Zggis/micromouse-3d/maze/supports/elevated-cell_61.STEP

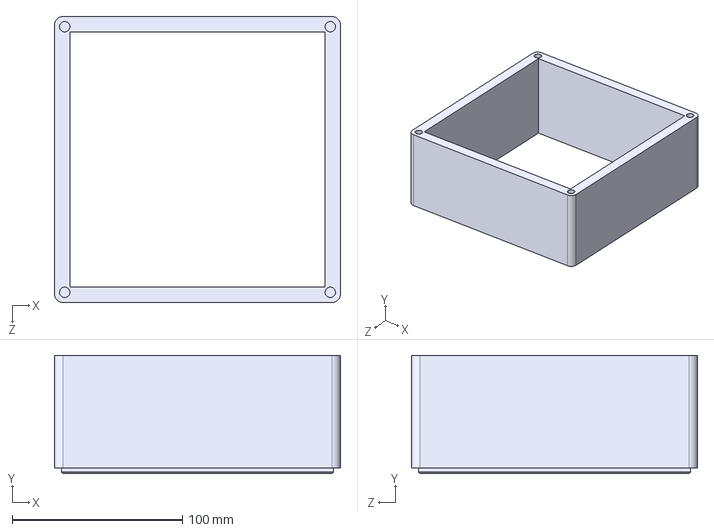
[picture p39: CAD file, 2026-06-22]
maze/supports/elevated-cell_61.STEP
168.0 x 69.4 x 168.0 mm
