Zggis/micromouse-3d/rules/pyramid.STL

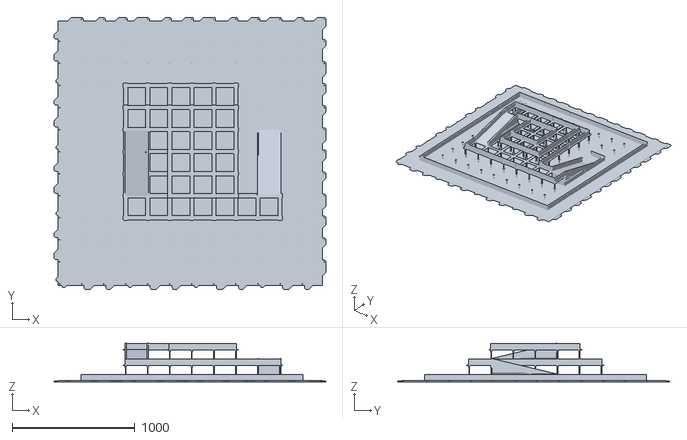
[picture p41: CAD file, 2026-09-28]
rules/pyramid.STL
2220.0 x 2220.0 x 317.4
