Zggis/micromouse-3d/maze/lattice/vertex_61.STEP

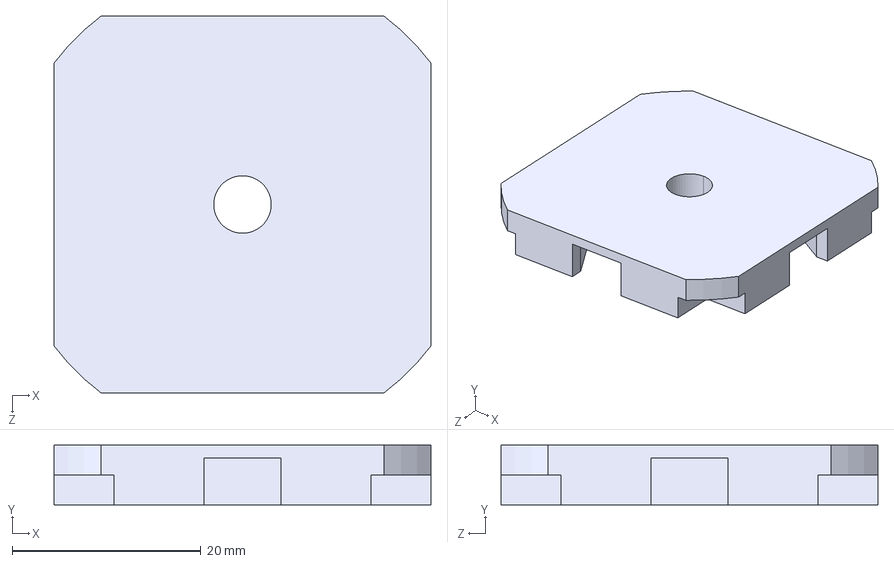
[picture p42: CAD file, 2026-06-22]
maze/lattice/vertex_61.STEP
40.0 x 6.35 x 40.0 mm
