Zggis/micromouse-3d/maze/ramp/ramp-middle-frame_62.STEP

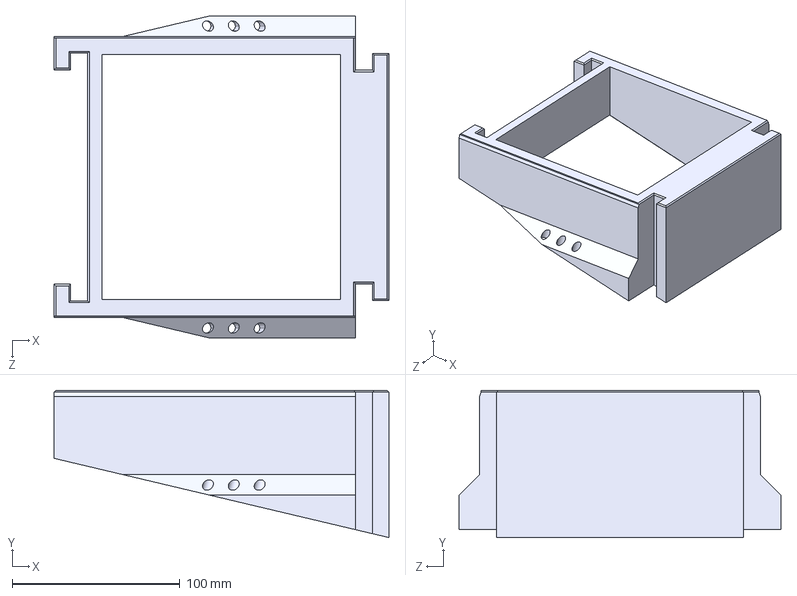
[picture p43: CAD file, 2026-07-10]
maze/ramp/ramp-middle-frame_62.STEP
199.6 x 87.7 x 192.0 mm
