Zggis/micromouse-3d/maze/supports/elevated-cell-top_61.STEP

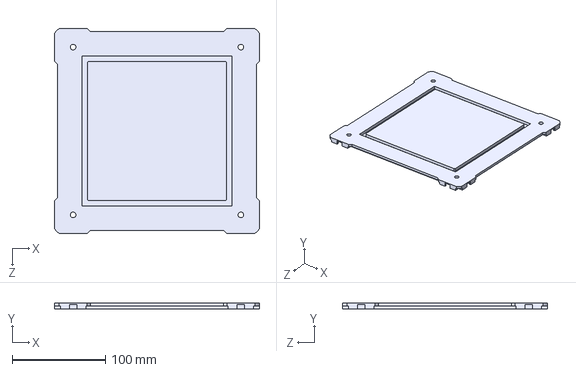
[picture p44: CAD file, 2026-06-22]
maze/supports/elevated-cell-top_61.STEP
220.0 x 6.35 x 220.0 mm
