Zggis/micromouse-3d/maze/walls/ramp-wall-upper.STEP

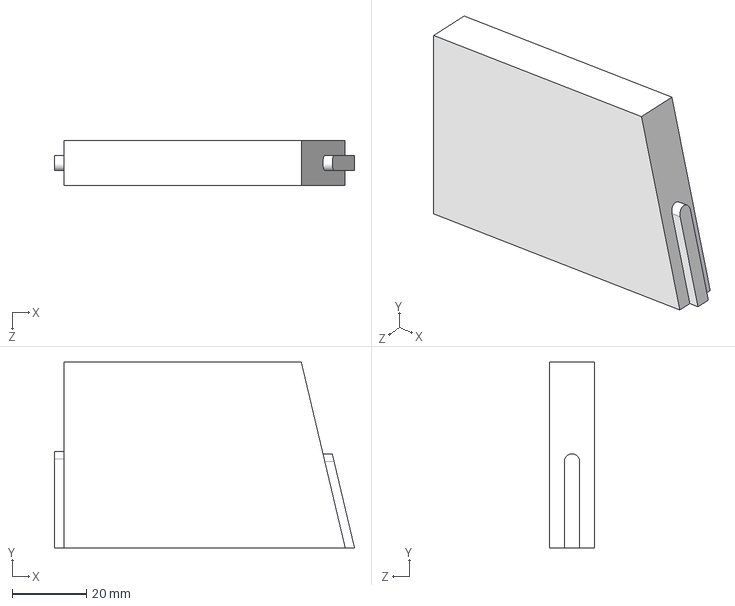
[picture p45: CAD file, 2026-06-22]
maze/walls/ramp-wall-upper.STEP
80.8 x 50.0 x 12.0 mm
