Zggis/micromouse-3d/maze/ramp/ramp-middle_62.STEP

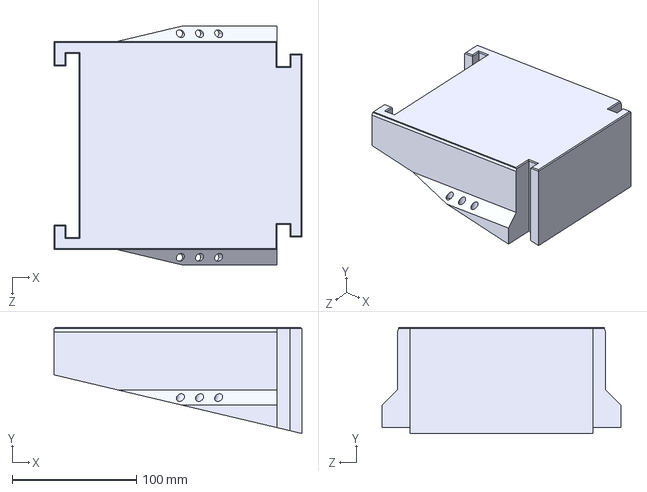
[picture p46: CAD file, 2026-07-10]
maze/ramp/ramp-middle_62.STEP
199.6 x 85.3 x 192.0 mm
