Zggis/micromouse-3d/maze/special/ramp-wall-half_60.STEP

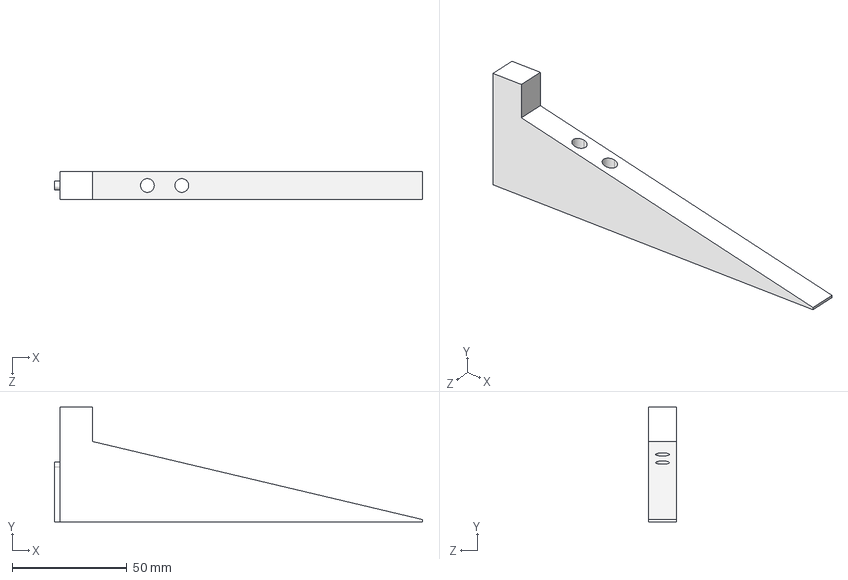
[picture p47: CAD file, 2026-06-22]
maze/special/ramp-wall-half_60.STEP
160.4 x 50.0 x 12.0 mm
