Zggis/micromouse-3d/maze/walls/ramp-wall-lower_62.STEP

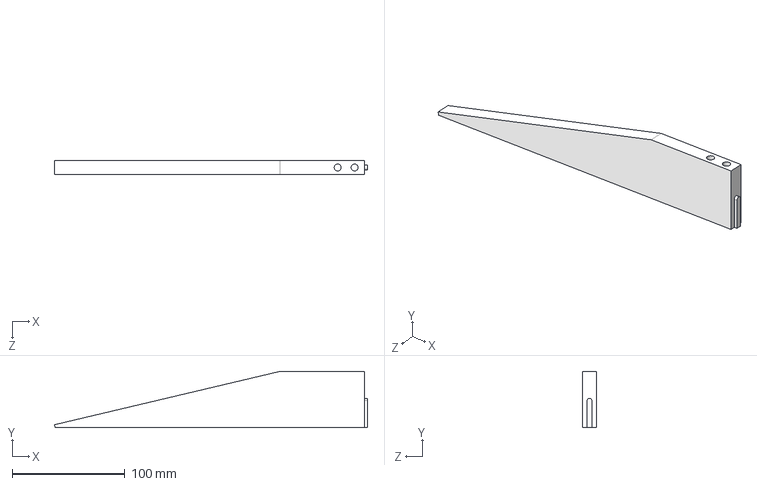
[picture p48: CAD file, 2026-06-22]
maze/walls/ramp-wall-lower_62.STEP
277.9 x 50.0 x 12.0 mm
