Zggis/micromouse-3d/maze/ramp/ramp-upper-frame_60.STEP

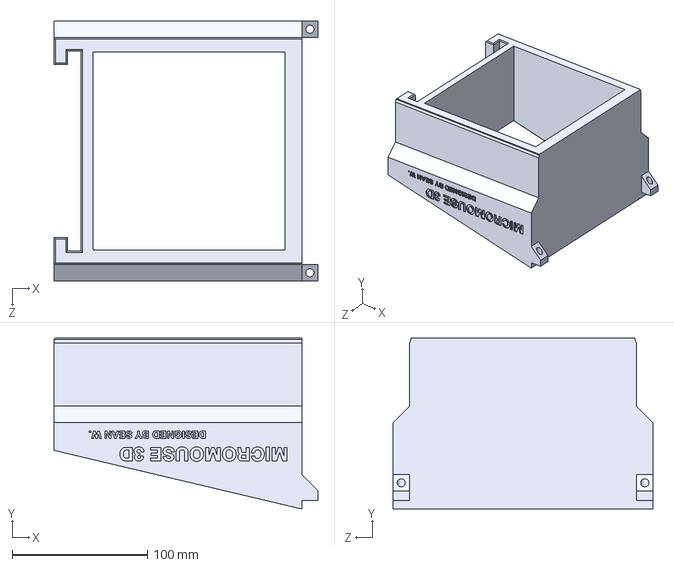
[picture p49: CAD file, 2026-07-10]
maze/ramp/ramp-upper-frame_60.STEP
195.1 x 126.3 x 192.0 mm
