Zggis/micromouse-3d/maze/special/ramp-wall-lower-hole_62.STEP

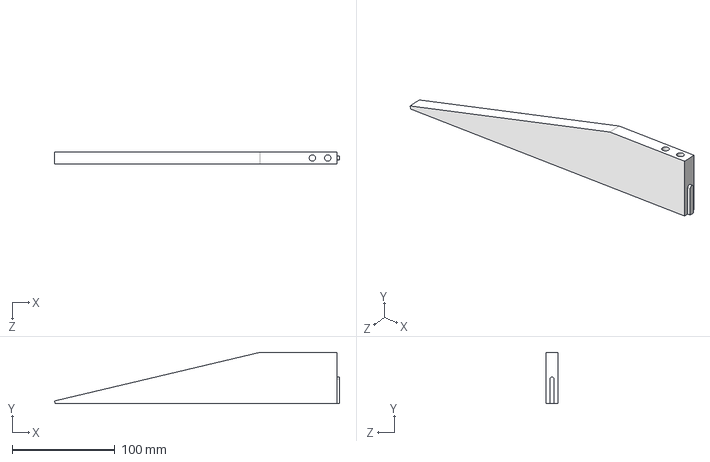
[picture p50: CAD file, 2026-06-22]
maze/special/ramp-wall-lower-hole_62.STEP
277.9 x 50.0 x 12.0 mm
