Zggis/micromouse-3d/maze/edges/connector-edge.STEP

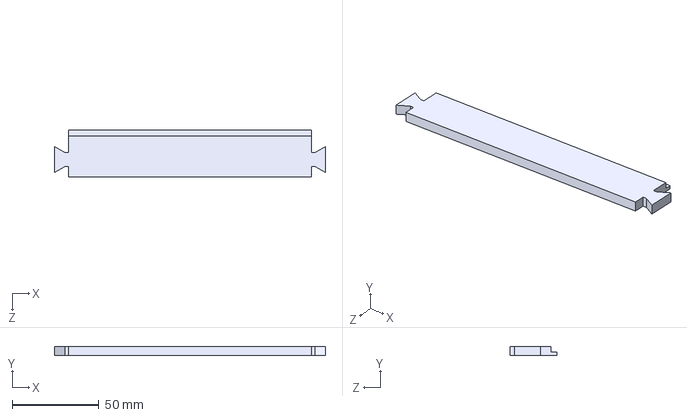
[picture p51: CAD file, 2026-06-22]
maze/edges/connector-edge.STEP
155.8 x 5.00 x 27.0 mm
