Zggis/micromouse-3d/maze/supports/elevated-cell-base_62.STEP

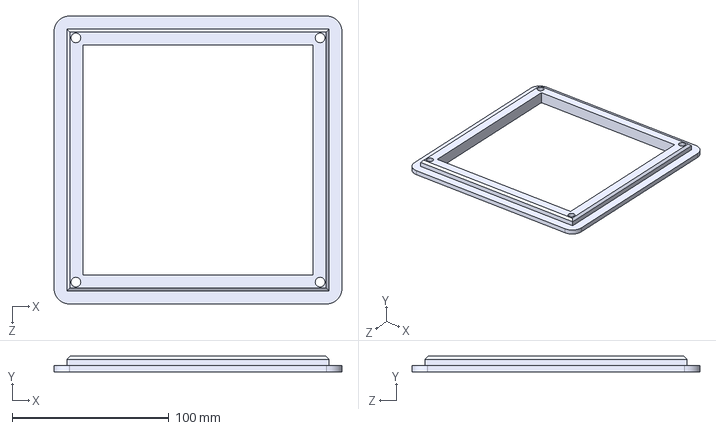
[picture p52: CAD file, 2026-06-22]
maze/supports/elevated-cell-base_62.STEP
184.0 x 10.0 x 184.0 mm
