Zggis/micromouse-3d/maze/walls/pillar_62.STEP

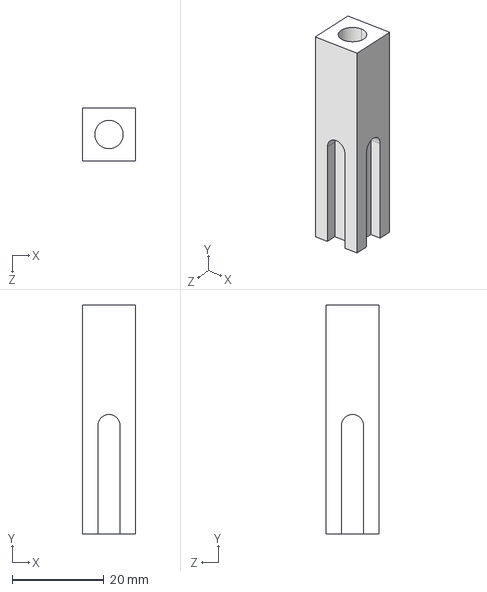
[picture p53: CAD file, 2026-06-22]
maze/walls/pillar_62.STEP
11.5 x 50.0 x 11.5 mm
