Zggis/micromouse-3d/maze/ramp/ramp-lower-frame.STEP

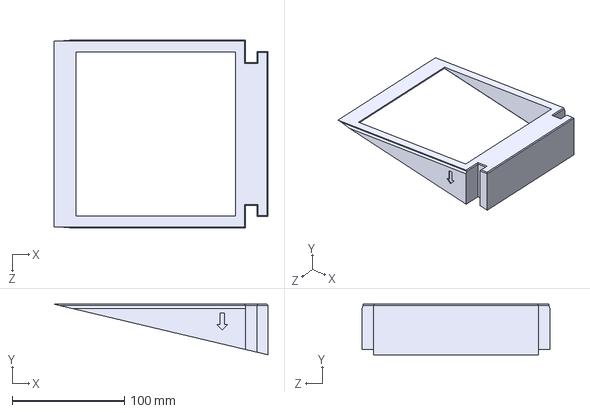
[picture p54: CAD file, 2026-07-10]
maze/ramp/ramp-lower-frame.STEP
190.9 x 45.2 x 167.6 mm
